pe1mew/PanelMeterClock/Design/notes.md

Option 1: PWM + RC Low-pass Filter (Simplest)
The ESP32-S3's LEDC peripheral has 8 channels — use 3 of them with PWM + RC filter per channel.

Hardware: 3× resistor + capacitor per channel (~1kΩ + 10µF typical)
Pros: Zero extra ICs, easy software, GPIO-flexible
Cons: Some ripple on the output; filter adds settling time; voltage limited to 3.3V
Good fit: Panel meters are slow/mechanical — ripple won't matter much if filter cutoff is low enough (e.g., ~10Hz)

we are going to write a functional specification for a clock that uses 3 analog panel meters to show the actual time. one meter will show hour of day on a scale from 0 to 24, one meter will show minute of day from 0 to 60, and one meter will show second of day on a scale from 0 to 60. At power on, the clock will start showing 0:00:00 and seconds increment like a normal clock. this is intial phase, in the second phase the clock will try to acquire NTP time over a wifi connection. if that fails clock will attempt endless in a 15 second interval. after NTP fails or succedded in the third phase the GNSS receiver is watched. If the GNSS receiver is presenting valid time, this will override NTP. 1PPS signal will be source for 1 second step, and will be sythesized if GNSS is not available from NTP. the clock will determine daylight saving and switch automatically using location derived from internet connection (prio 2) or from GNSS information (Prio 1). The clock will expose a WiFi AP when no connection is available to a WiFi AP. It will expose a web gui to calibrate each panel meter individually, configure the WiFi network to which it shall connect (only DHCP), enable GNSS use, and a status screen of the clock. There is no password required. teh wifi portal exposes a FOTA service to upload new firmware. Firmware is authenticated through the use of asymmetrical keys.

Add that only local time based upon location is displayed. not UTC.
Add that the software will run FreeRTOS.
Add that the meters will bemodified by replacing the series resistor for one where full scale equals 3 Volt. (the instrument is a 1V full-scal instrument.

the owl, for wisdom and the passage of time,
Hummingbirds are renowned for their precise and rapid movements, hovering in place with extraordinary control as they feed from flowers.
Their wingbeats are astonishingly regular—many species beat their wings at a rate of around 50 times per second.
They keep a rigorous feeding schedule, visiting hundreds of flowers daily and remembering the exact timing of each bloom’s nectar replenishment.
