pe1mew/PanelMeterClock/Documentation/notes.md

# Documentation Index

## Panel Meter — Siemens 1604P (DC10.00GF024T005)

- `0900766b8147dbe5.pdf` — Siemens 1604P product documentation (part 1)
- `0900766b8147dbe7.pdf` — Siemens 1604P product documentation (part 2)
- `0900766b8147dbea.pdf` — Siemens 1604P product documentation (part 3)

## GNSS Module — Quectel L76-M33

Documentation files to be added when received from Quectel.
