pe1mew/PanelMeterClock/Hardware/KiCad/panelMeterClock/panelMeterClock.kicad_sch

## KiCad design Hardware/KiCad/panelMeterClock/panelMeterClock.kicad_sch (2026-06-16, an earlier design)

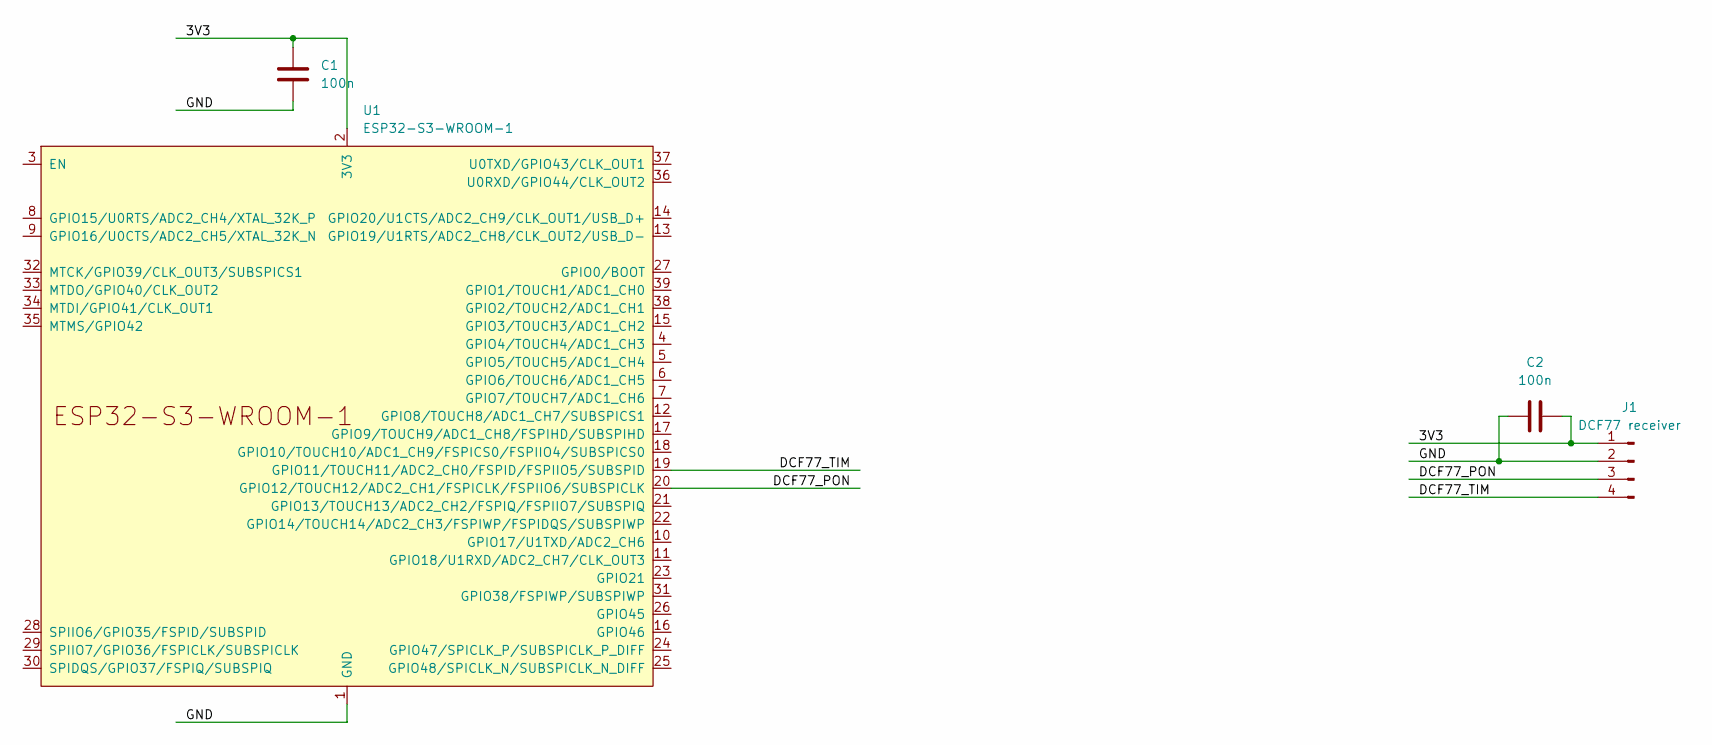
[picture p3: schematic panelMeterClock.kicad_sch]

Parts:
C1, C2: 100n
J1: DCF77 receiver
U1: ESP32-S3-WROOM-1

Connections:
3V3: C1.1, C2.2, J1.1, U1.2 (3V3)
DCF77_PON: J1.3, U1.20 (GPIO12/TOUCH12/ADC2_CH1/FSPICLK/FSPIIO6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)
DCF77_TIM: J1.4, U1.19 (GPIO11/TOUCH11/ADC2_CH0/FSPID/FSPIIO5/S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)
GND: C1.2, C2.1, J1.2, U1.1 (GND), U1.40 (GND), U1.41 (GND)
